hytech-racing/circuits-2023/External Diagrams/External Diagram FSAE 2022.sch

## EAGLE design External Diagrams/External Diagram FSAE 2022.sch (2022-06-23)

Schematic: External Diagram FSAE 2022.sch

Parts:
ACCUMULATOR_INDICATOR_LIGHT: LED_0603_RED; 0603-LED
J1, J4: CONNECTOR-22_SOURIAU_; SOURIAU_12-35
J15, J16: CONNECTOR-6_NF_T_V_BLACK; MOLEX_NANOFIT_PTH_06

Notes on the sheet:
Accumulator Container
Left Rear Panel
Right Rear Panel
12AWG chassis grounding per FH EV4.1.4
Wire Key Thin Green: GLV Blue: GLV Buses Thick Green: HV Orange: HV High Current Path
Main Electronic/ Telemetry Control Unit
HyTech Racing 2022 FSAE Electrical Diagram
Pedal Box
Firewall
Dashboard
Power Switching Board
TSAL
USB
START_BUTTON
8STA60435SN
8STA60435SA
8STA60435PN
8STA60435PA
BRAKE_1
BRAKE_2
PEDAL_1
PEDAL_2
8STA60435SB
8STA60435PB
PEDAL_3
GND_RADIATOR
GND_CHASSIS
HVD
